hmd245/smart_farm/plugins/PHPExcel-1.8/Documentation/markdown/Overview/images/09-command-line-calculation.png

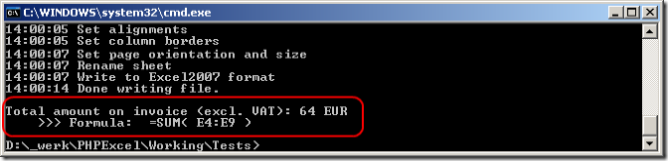
plugins/PHPExcel-1.8/Documentation/markdown/Overview/images/09-command-line-calculation.png
