hmd245/smart_farm/plugins/PHPExcel-1.8/Documentation/assets/ClassDiagrams/Architecture.png

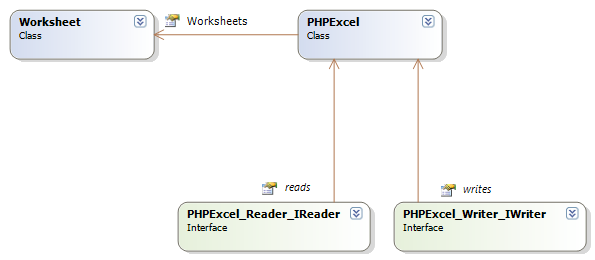
plugins/PHPExcel-1.8/Documentation/assets/ClassDiagrams/Architecture.png
