hmd245/smart_farm/plugins/PHPExcel-1.8/Documentation/assets/ClassDiagrams/ReaderWriter.png

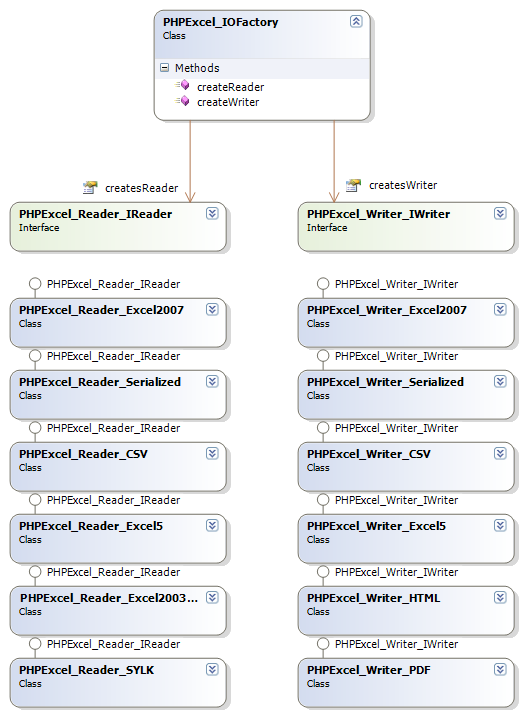
plugins/PHPExcel-1.8/Documentation/assets/ClassDiagrams/ReaderWriter.png
