hmd245/smart_farm/plugins/PHPExcel-1.8/Documentation/markdown/Features/Autofilters/images/01-01-autofilter.png

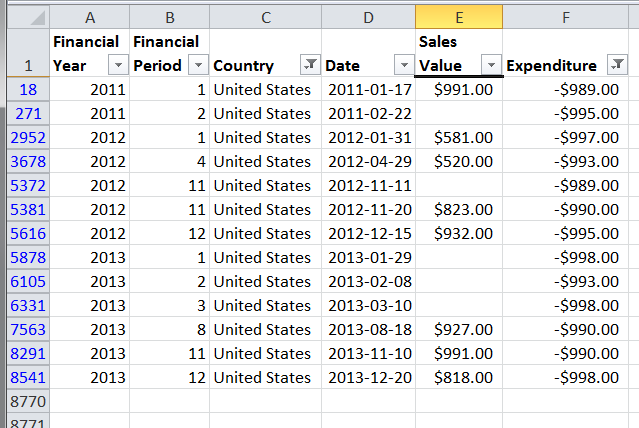
plugins/PHPExcel-1.8/Documentation/markdown/Features/Autofilters/images/01-01-autofilter.png
