hmd245/smart_farm/plugins/PHPExcel-1.8/Documentation/markdown/Features/Autofilters/images/01-02-autofilter.png

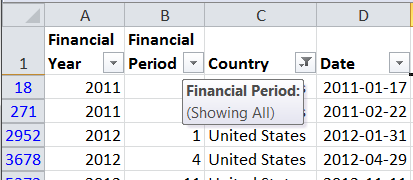
plugins/PHPExcel-1.8/Documentation/markdown/Features/Autofilters/images/01-02-autofilter.png
