hmd245/smart_farm/plugins/PHPExcel-1.8/Documentation/markdown/Features/Autofilters/images/04-01-simple-autofilter.png

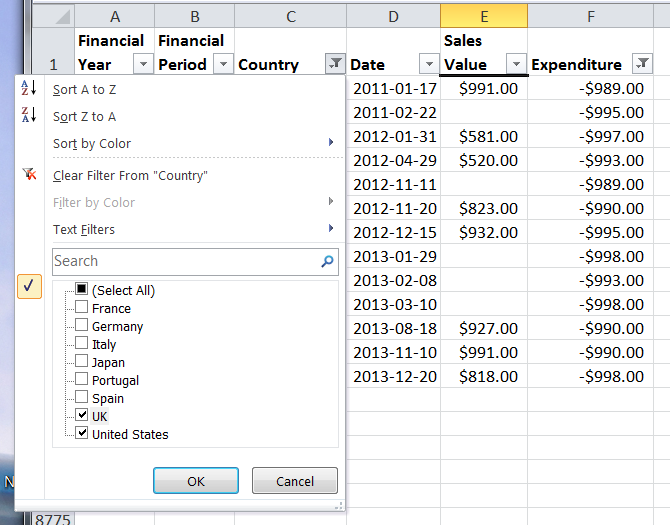
plugins/PHPExcel-1.8/Documentation/markdown/Features/Autofilters/images/04-01-simple-autofilter.png
