hmd245/smart_farm/plugins/PHPExcel-1.8/Documentation/markdown/Features/Autofilters/images/04-04-dynamic-autofilter.png

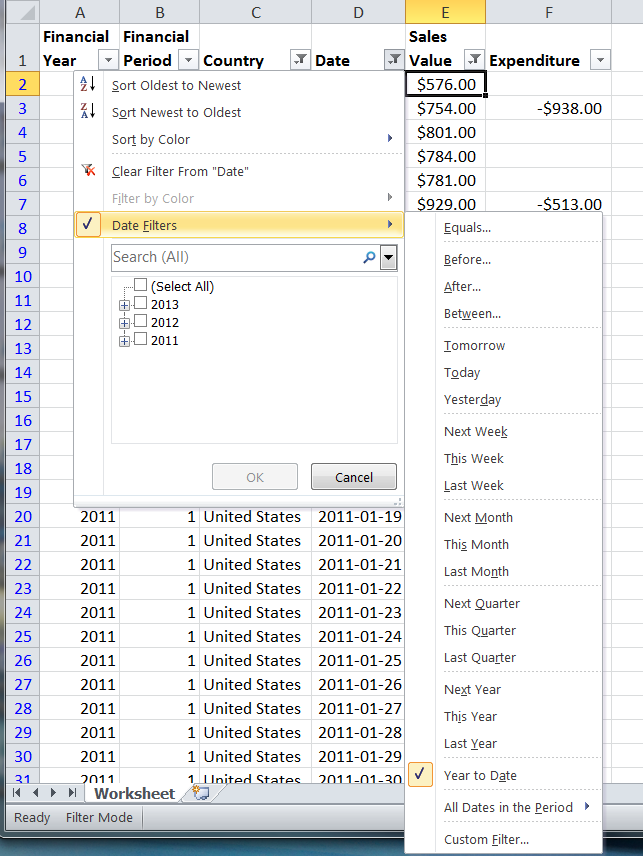
plugins/PHPExcel-1.8/Documentation/markdown/Features/Autofilters/images/04-04-dynamic-autofilter.png
