hmd245/smart_farm/plugins/PHPExcel-1.8/Documentation/markdown/Features/Autofilters/images/04-05-topten-autofilter-1.png

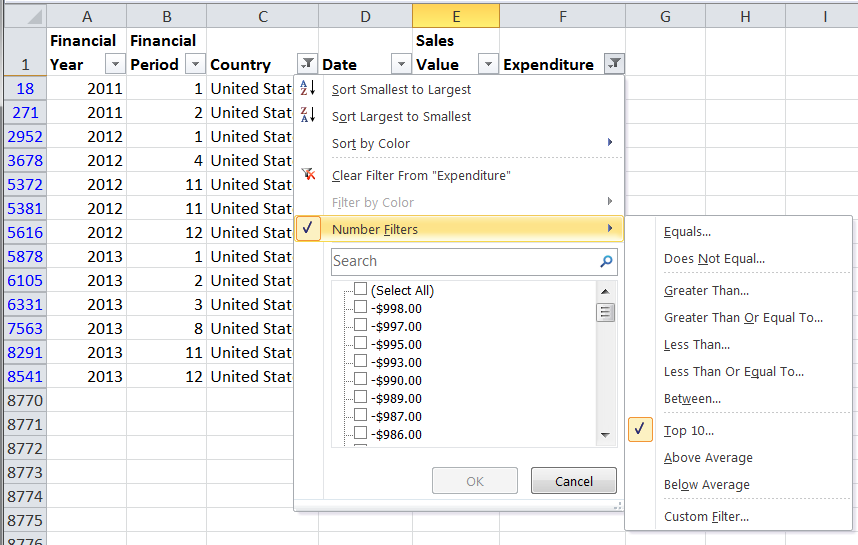
plugins/PHPExcel-1.8/Documentation/markdown/Features/Autofilters/images/04-05-topten-autofilter-1.png
