hmd245/smart_farm/plugins/PHPExcel-1.8/Documentation/markdown/Overview/images/07-simple-example-3.png

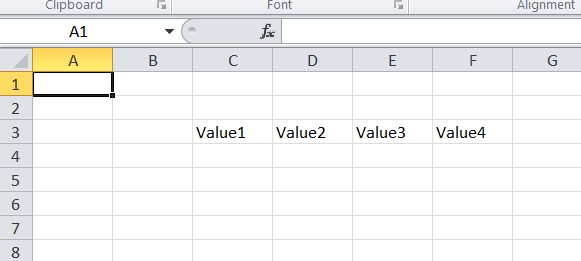
plugins/PHPExcel-1.8/Documentation/markdown/Overview/images/07-simple-example-3.png
