hmd245/smart_farm/plugins/PHPExcel-1.8/Documentation/markdown/Overview/images/08-cell-comment.png

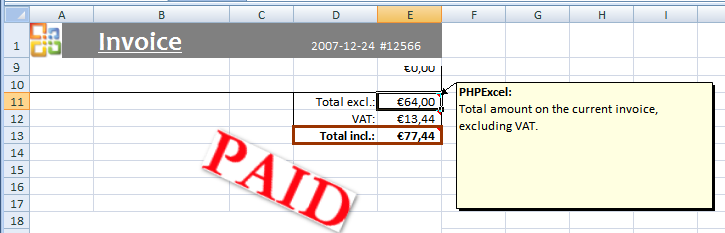
plugins/PHPExcel-1.8/Documentation/markdown/Overview/images/08-cell-comment.png
