hmd245/smart_farm/plugins/PHPExcel-1.8/Documentation/markdown/Overview/images/09-formula-in-cell-1.png

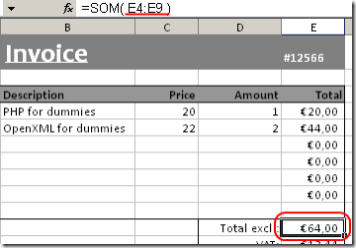
plugins/PHPExcel-1.8/Documentation/markdown/Overview/images/09-formula-in-cell-1.png
