hmd245/smart_farm/plugins/PHPExcel-1.8/Documentation/markdown/Overview/images/08-page-setup-scaling-options.png

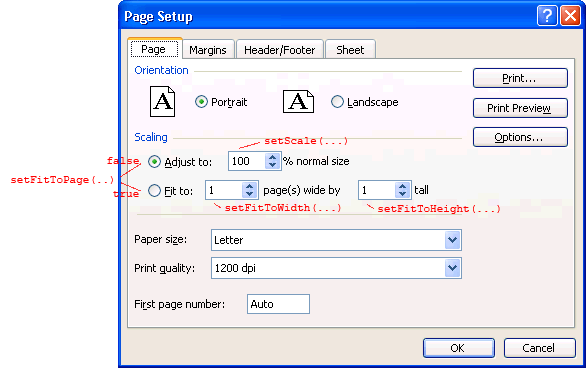
plugins/PHPExcel-1.8/Documentation/markdown/Overview/images/08-page-setup-scaling-options.png
